lowdrant/kyber/hw/KyberBoard/doc-imgs/MMA8452Q-AppSch.png

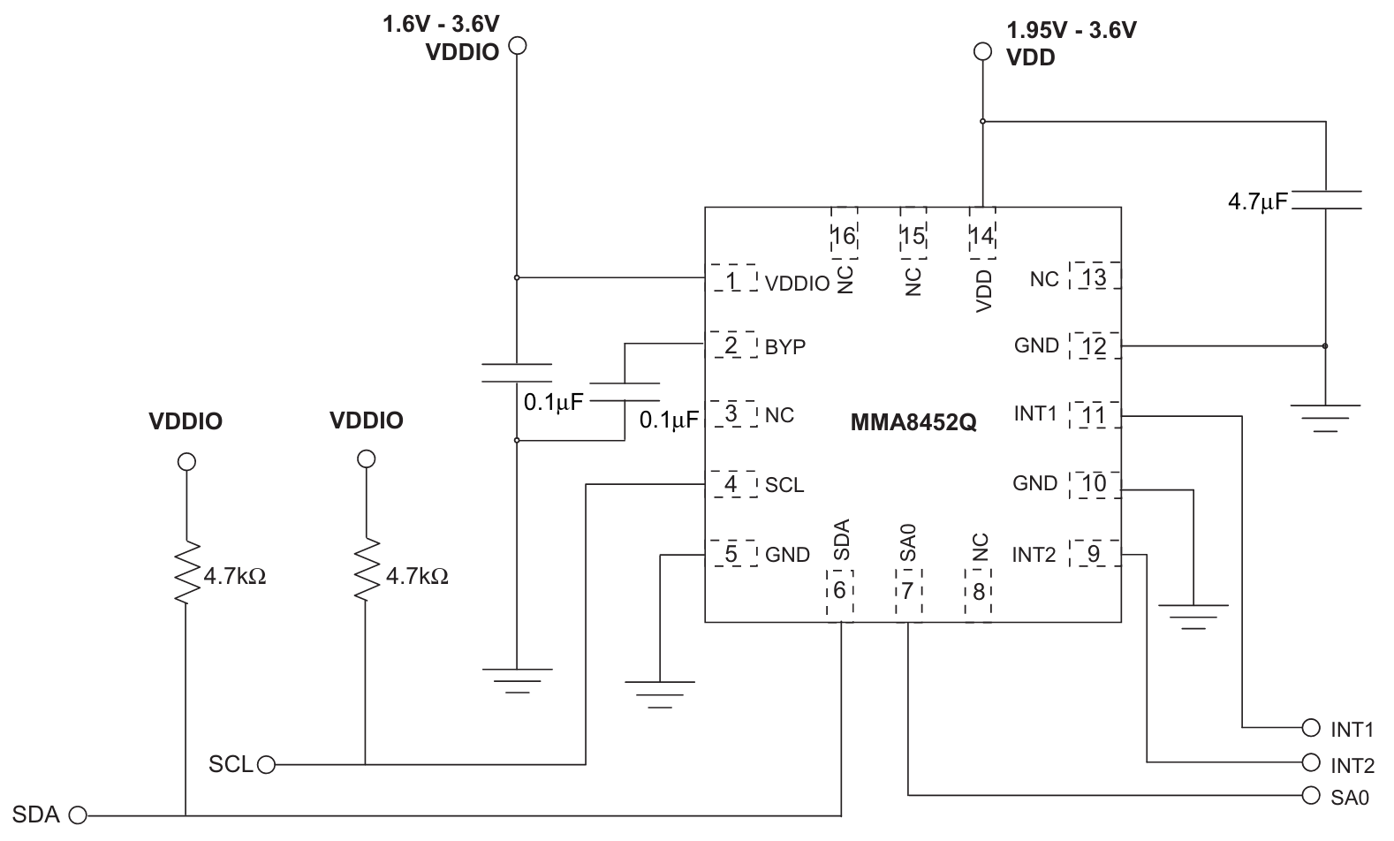
hw/KyberBoard/doc-imgs/MMA8452Q-AppSch.png
