lowdrant/kyber/hw/KyberBoard/doc-imgs/simNMOSSwitching.png

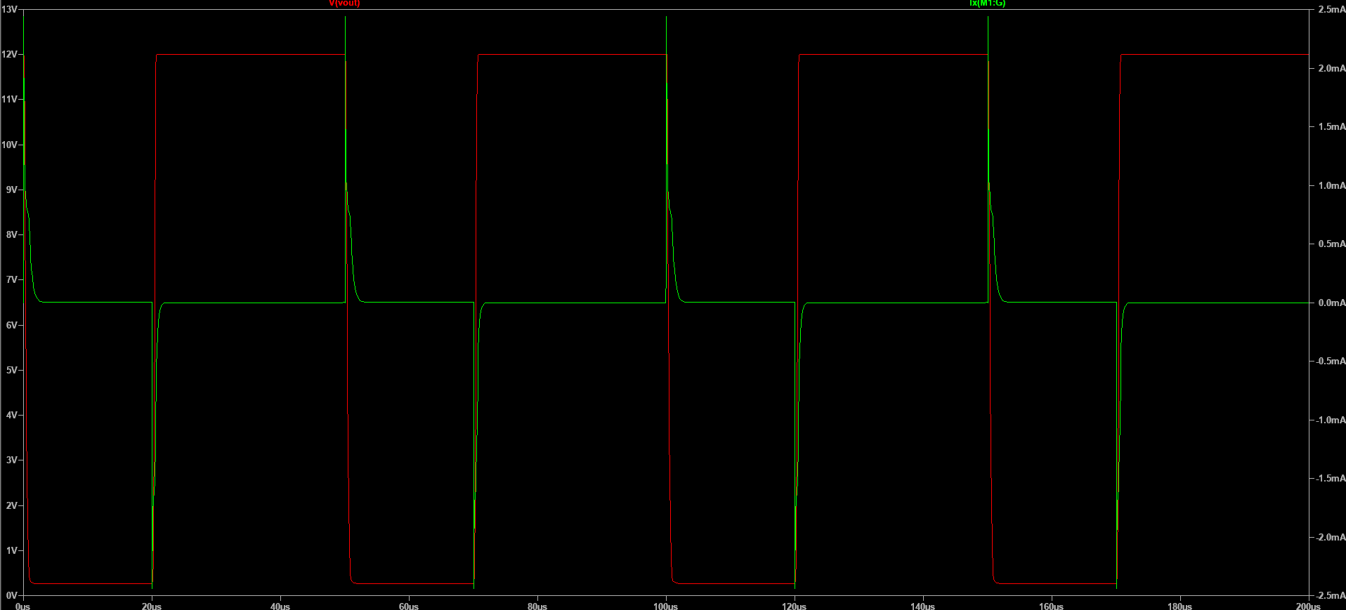
hw/KyberBoard/doc-imgs/simNMOSSwitching.png
