lowdrant/kyber/hw/KyberBoard/easter-eggs/clankryze.png

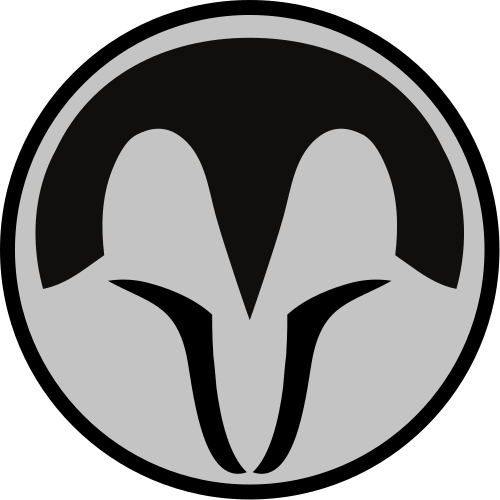
hw/KyberBoard/easter-eggs/clankryze.png
