lowdrant/kyber/hw/KyberBoard/easter-eggs/lukevader-edit.png

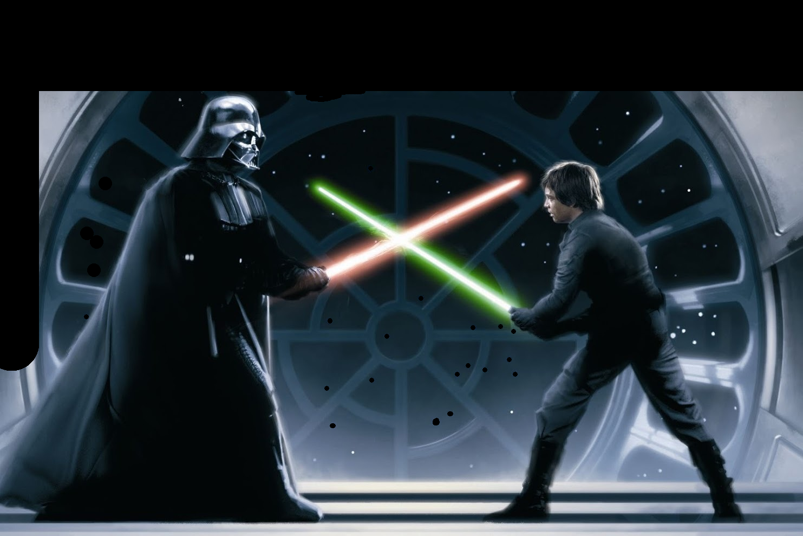
hw/KyberBoard/easter-eggs/lukevader-edit.png
