lowdrant/kyber/hw/KyberBoard/easter-eggs/lukevader.jpg

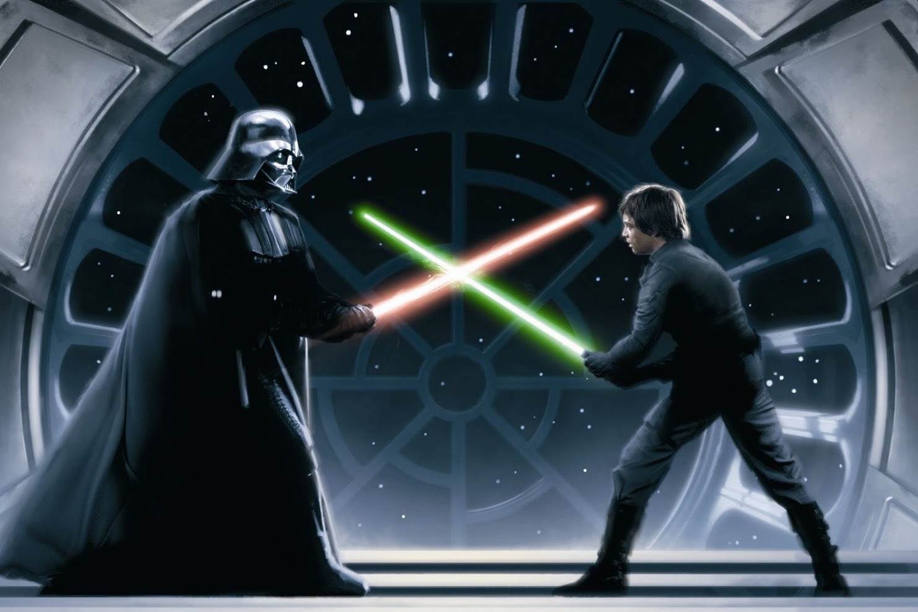
hw/KyberBoard/easter-eggs/lukevader.jpg
