lowdrant/kyber/hw/KyberBoard/easter-eggs/saber.png

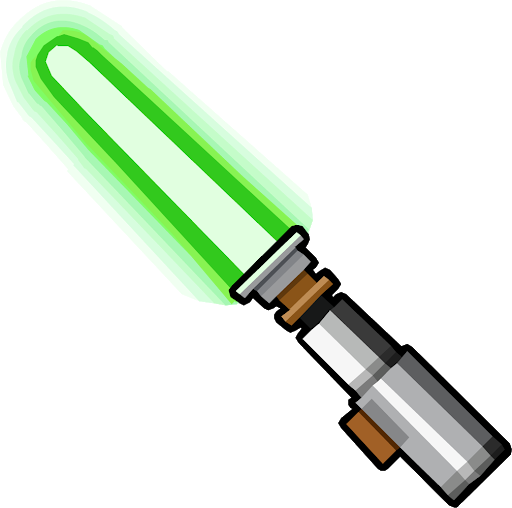
hw/KyberBoard/easter-eggs/saber.png
