lowdrant/kyber/cad/saber-base/files/Luke_Skywalker_EP6_-_Upper_Copper_Coupling.STL

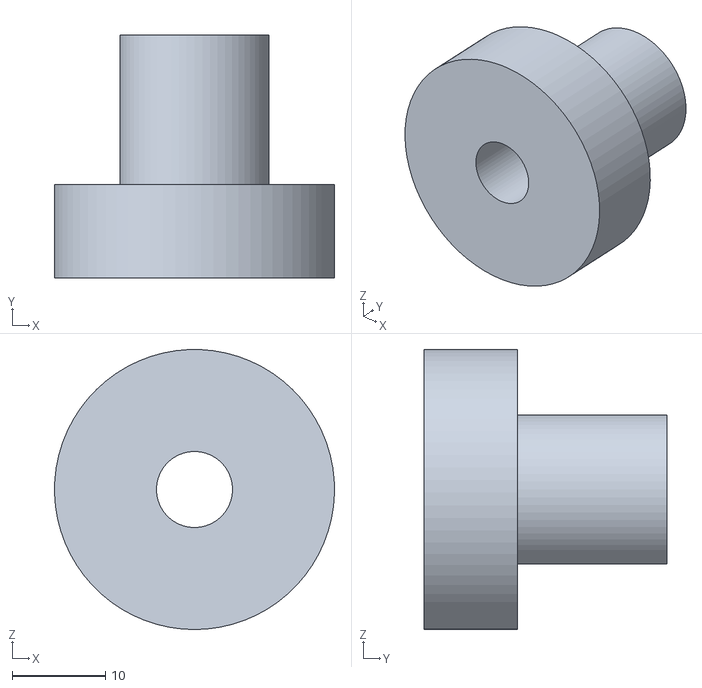
[picture p32: CAD file, 2021-05-16]
cad/saber-base/files/Luke_Skywalker_EP6_-_Upper_Copper_Coupling.STL
30.0 x 26.0 x 30.0
