lowdrant/kyber/cad/saber-base/files/Luke_Skywalker_EP6_-_Grip.STL

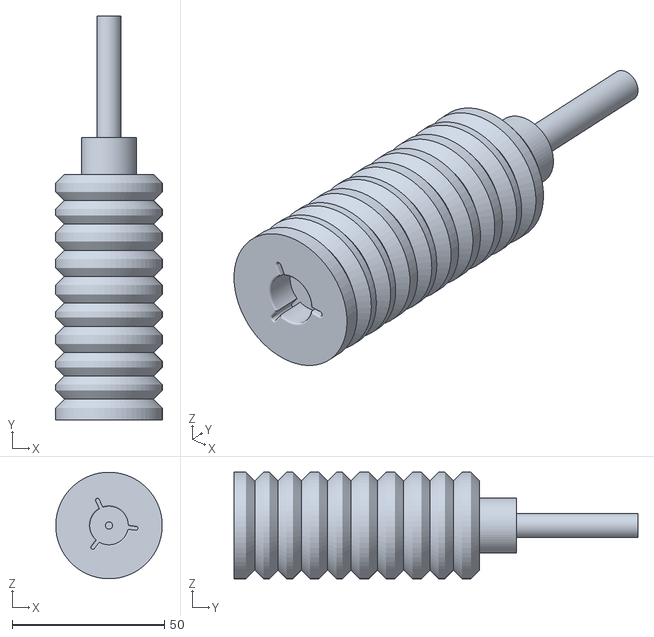
[picture p33: CAD file, 2021-05-16]
cad/saber-base/files/Luke_Skywalker_EP6_-_Grip.STL
35.0 x 132.7 x 35.0
