lowdrant/kyber/cad/saber-base/files/Luke_Skywalker_EP6_-_Emitter_Nipple.STL

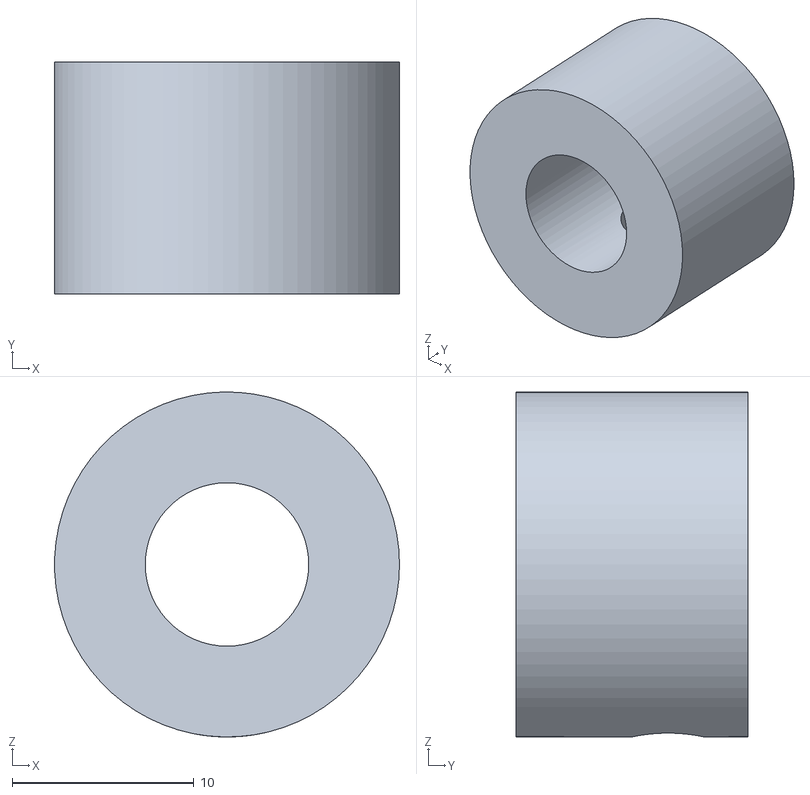
[picture p34: CAD file, 2021-05-16]
cad/saber-base/files/Luke_Skywalker_EP6_-_Emitter_Nipple.STL
19.0 x 12.8 x 19.0
