lowdrant/kyber/cad/saber-base/files/Luke_Skywalker_EP6_-_Luke_Emitter.STL

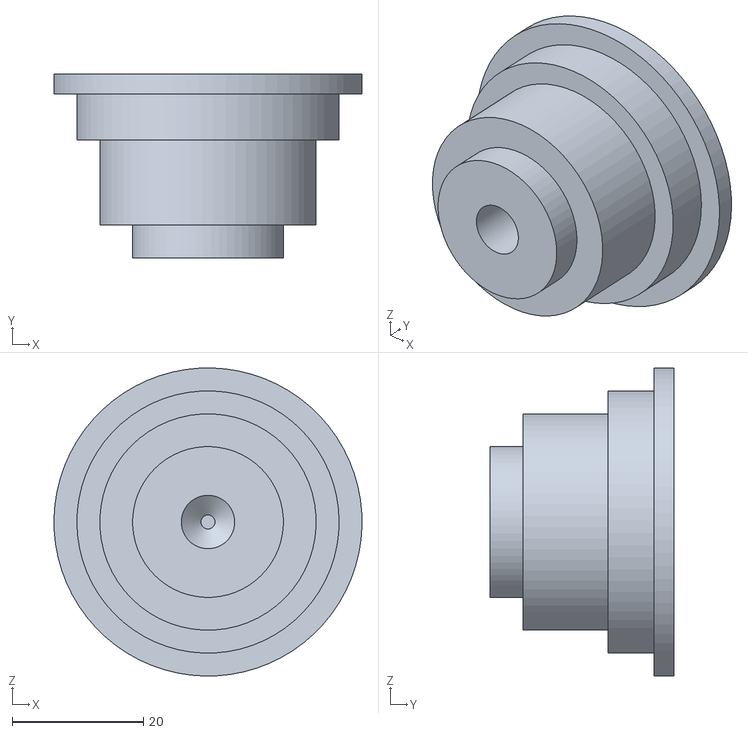
[picture p35: CAD file, 2021-05-16]
cad/saber-base/files/Luke_Skywalker_EP6_-_Luke_Emitter.STL
47.0 x 28.0 x 47.0
