lowdrant/kyber/cad/saber-base/files/EP6_Luke_Midsection_Solid.STL

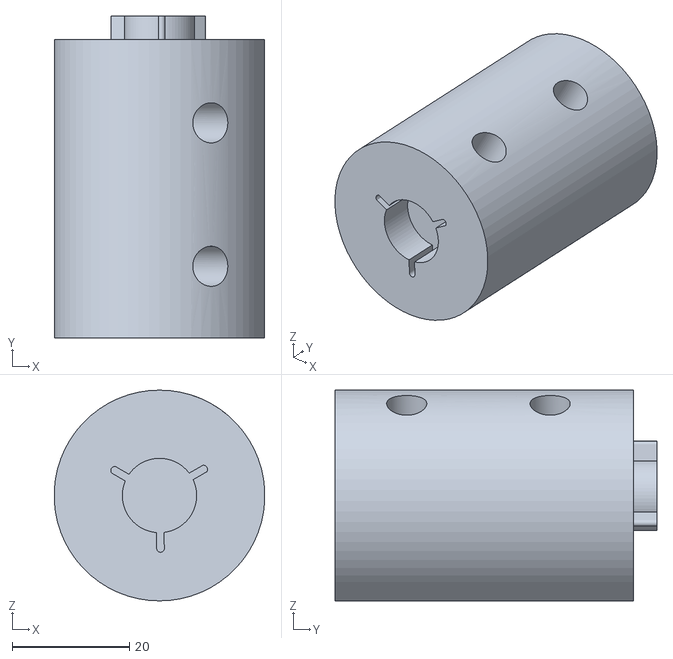
[picture p36: CAD file, 2021-05-16]
cad/saber-base/files/EP6_Luke_Midsection_Solid.STL
36.0 x 55.0 x 36.0
