lowdrant/kyber/cad/saber-base/files/Luke_Skywalker_EP6_-_Switch_Casing.STL

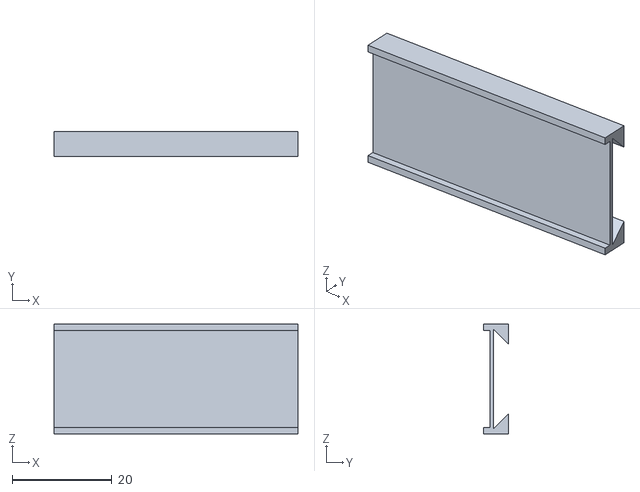
[picture p37: CAD file, 2021-05-16]
cad/saber-base/files/Luke_Skywalker_EP6_-_Switch_Casing.STL
49.0 x 5.00 x 22.0
