lowdrant/kyber/cad/saber-base/files/Luke_Skywalker_EP6_-_Midsection.STL

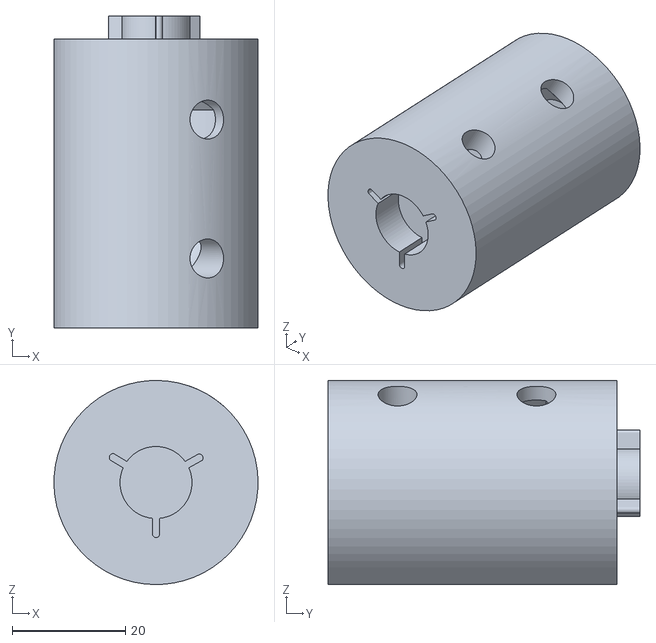
[picture p38: CAD file, 2021-05-16]
cad/saber-base/files/Luke_Skywalker_EP6_-_Midsection.STL
36.0 x 55.0 x 36.0
