lowdrant/kyber/cad/saber-base/files/Luke_Skywalker_EP6_-_Switch.STL

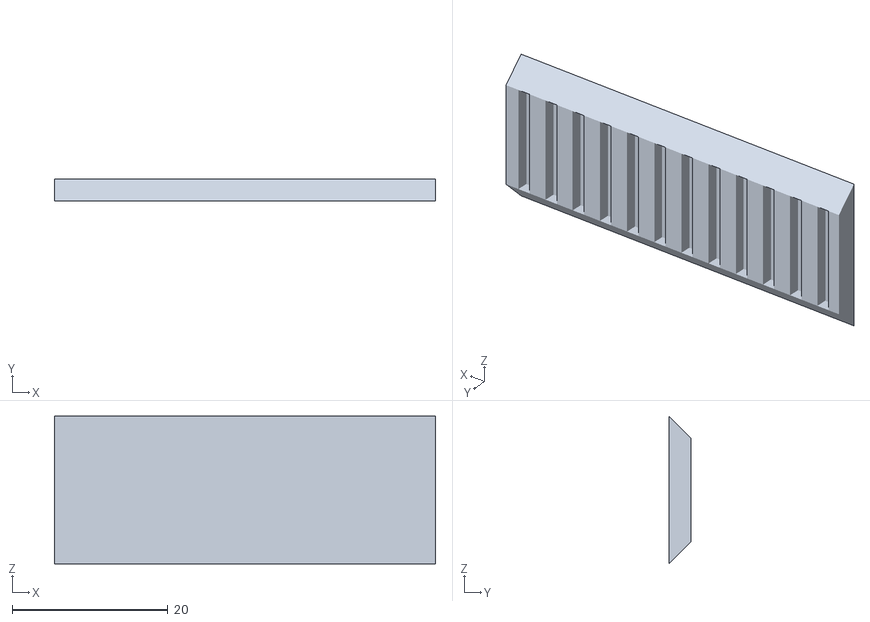
[picture p39: CAD file, 2021-05-16]
cad/saber-base/files/Luke_Skywalker_EP6_-_Switch.STL
49.0 x 2.85 x 19.0
