lowdrant/kyber/cad/saber-base/files/Luke_Skywalker_EP6_-_Pommel.STL

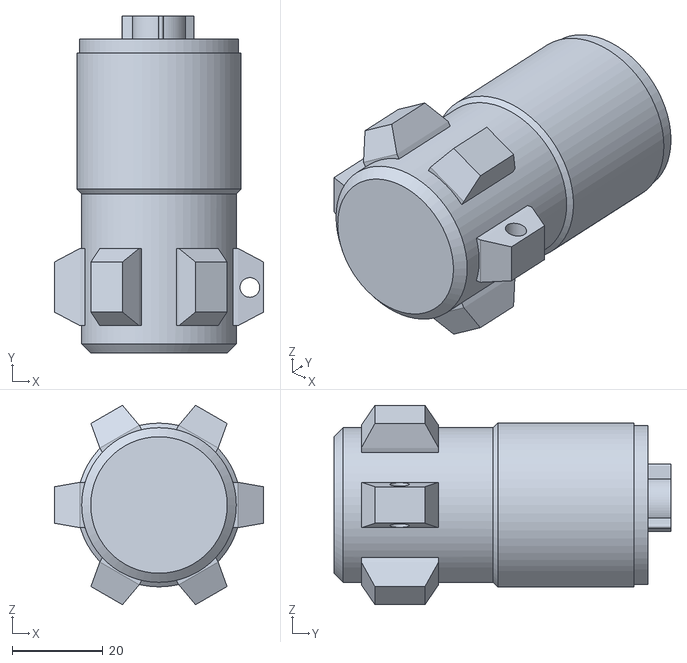
[picture p40: CAD file, 2021-05-16]
cad/saber-base/files/Luke_Skywalker_EP6_-_Pommel.STL
46.0 x 74.1 x 43.8
