lowdrant/kyber/cad/saber-base/files/Luke_Skywalker_EP6_-_Belt_Ring.STL

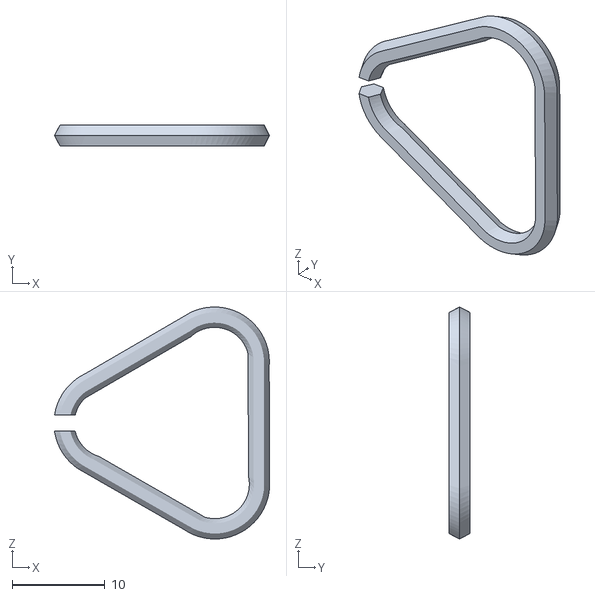
[picture p41: CAD file, 2021-05-16]
cad/saber-base/files/Luke_Skywalker_EP6_-_Belt_Ring.STL
23.2 x 2.28 x 25.0
