lowdrant/kyber/cad/saber-base/files/Luke_Skywalker_EP6_-__Switch_Lower.STL

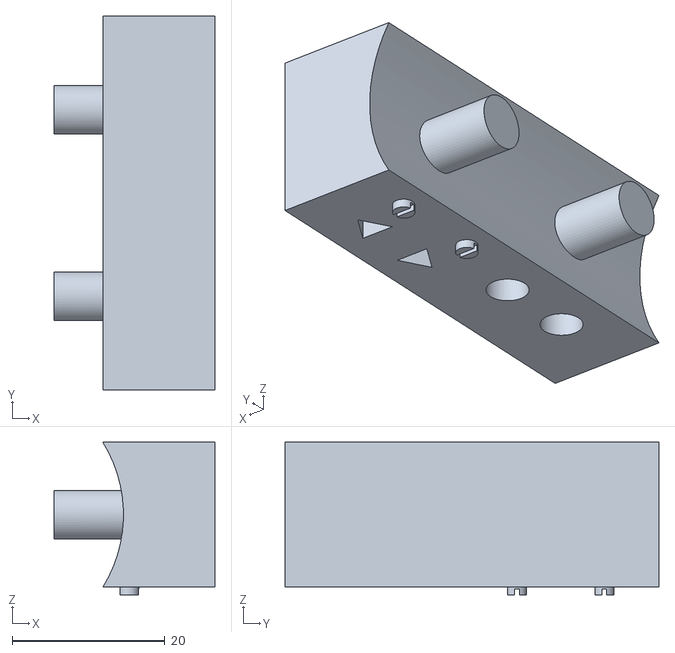
[picture p42: CAD file, 2021-05-16]
cad/saber-base/files/Luke_Skywalker_EP6_-__Switch_Lower.STL
21.1 x 49.0 x 20.0
