lowdrant/kyber/reference-manuals/motor.jpg

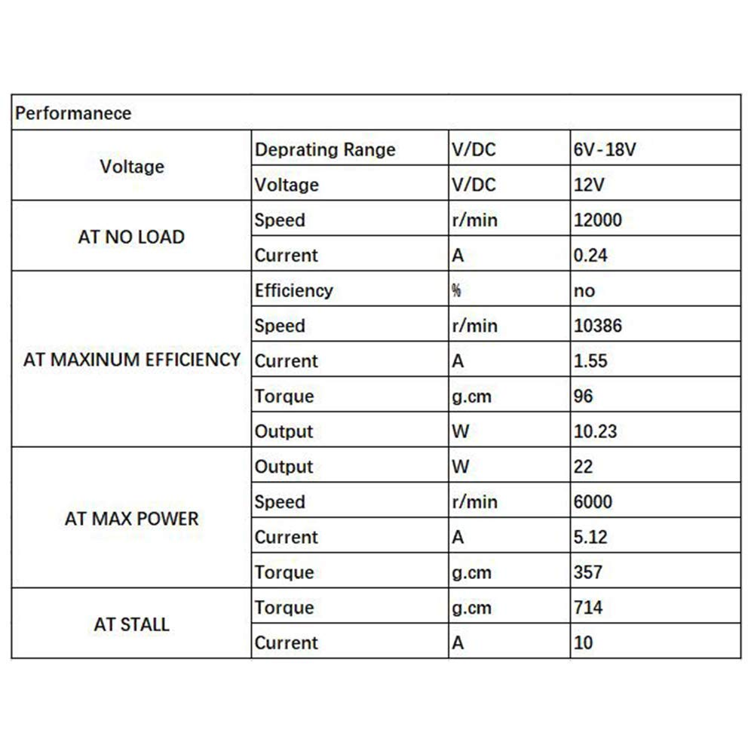
reference-manuals/motor.jpg
