lowdrant/kyber/hw/sims/testmyuv.asc

R1: res; 1
V1: voltage; PWL(0 -1 1 11)
X1: myuv
Named nets: 0
.tran 1
