lowdrant/kyber/hw/sims/mybatteryprotections.asc

D1: zener; MMBZ18VAL
D2: zener; DI_BZT52C8V2
M1: pmos; DMP3028LK3
M2: pmos; DMP3028LK3
M3: nmos; 2N7002
R1: res; 1k
R2: res; 0
R3: res; 1k
R4: res; 1k
Named nets: vg, Vout, Vrpp, Vbatt+, Vbatt-
.lib vendor-libs/DMP3028LK3.spice
.lib vendor-libs/BZT52C8V2.spice
