lowdrant/kyber/hw/sims/mysol.asc

L1: ind; 200m
R1: res; 13
Named nets: V+, V-
