lowdrant/kyber/hw/sims/myuv.asc

D2: zener; DI_BZT52C8V2
M1: nmos; NMOS_SSM3K337R
M2: pmos; DMP3028LK3
R3: res; 1k
R4: res; 1k
Named nets: Vout, V+, V-
.lib vendor-libs/DMP3028LK3.spice
.lib vendor-libs/BZT52C8V2.spice
.lib vendor-libs/SSM3K337R.lib
