lowdrant/kyber/hw/sims/power-systems.asc

D1: diode
R1: res; 5m
U1: INA181A1
V1: voltage; 3.3
Named nets: 0, 3v3, imtr
.tran 1 startup
.lib vendor-libs/ina181a1.lib
