lowdrant/kyber/hw/sims/pwmsol.asc

D1: diode; 1N4148
M1: nmos; NMOS_SSM3K337R
mysol: mysol
R2: res; 0
vpwm: voltage; PULSE(0 3.3 0 0 0 0.25 1); Rser=50
Vs: voltage; 12
Named nets: 0
.tran 4
.lib vendor-libs/DMTH4005SK3.spice
.lib vendor-libs/SSM3K337R.lib
