lowdrant/kyber/hw/sims/pwmspkr.asc

M1: nmos; NMOS_SSM3K337R
R2: res; 0
vpwm: voltage; PULSE(0 3.3 0 1n 1n 20u 50u); Rser=50
Vs: voltage; 12
X1: myspkr
Named nets: 0, vpwm, vout
.tran 200u
.lib vendor-libs/DMTH4005SK3.spice
.lib vendor-libs/SSM3K337R.lib
