lowdrant/kyber/hw/sims/mtr.asc

Lm: ind; 678.6m
Rm: res; 2.4
Named nets: VMTR-, VMTR+
