lowdrant/kyber/hw/sims/mybat.asc

R1: res; 0.96
V1: voltage; 15
Named nets: Vbatt+, Vbatt-
Battery Model for Sims
