lowdrant/kyber/hw/sims/bat-mtr.asc

Lm: ind; 678.6m
Rbat: res; 0.96
Rm: res; 2.4
Vbat: voltage; 7
Named nets: 0
.tran 1
