lowdrant/kyber/fw/holocron-libs/interface.h

/**
  ******************************************************************************
  * @file    interface.c
  * @author  Marion Anderson
  * @brief   TODO
  ******************************************************************************
  */

#ifndef INC_INTERFACE_H
#define INC_INTERFACE_H

#endif
